NTUEE-ESLab/2017Fall-SmartCameraCar/flask-video-streaming/frame.jpg

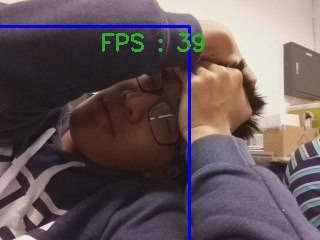
flask-video-streaming/frame.jpg
