NTUEE-ESLab/2017Fall-SmartCameraCar/Tracker_c_program/frame.jpg

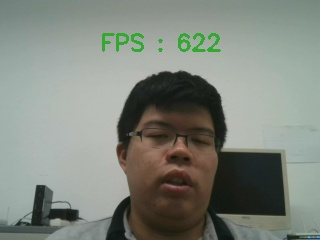
Tracker_c_program/frame.jpg
