NTUEE-ESLab/2017Fall-SmartCameraCar/webpage/images/automatic.jpg

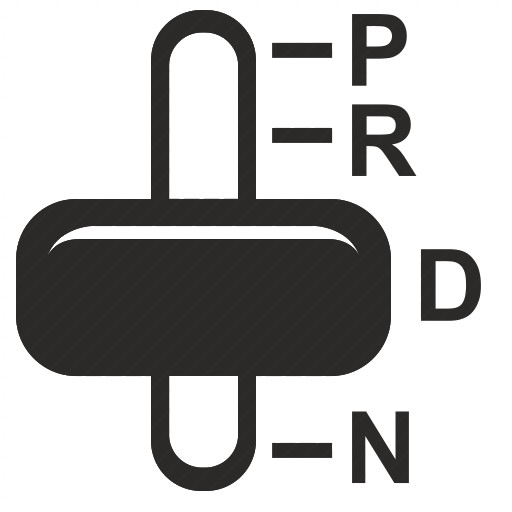
webpage/images/automatic.jpg
