NTUEE-ESLab/2017Fall-SmartCameraCar/webpage/images/cradle_head.jpg

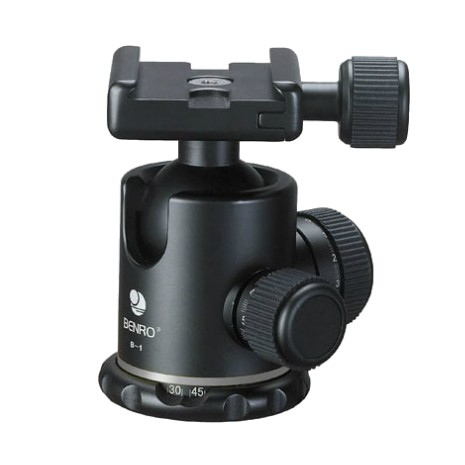
webpage/images/cradle_head.jpg
