NTUEE-ESLab/2017Fall-SmartCameraCar/webpage/images/cta01.jpg

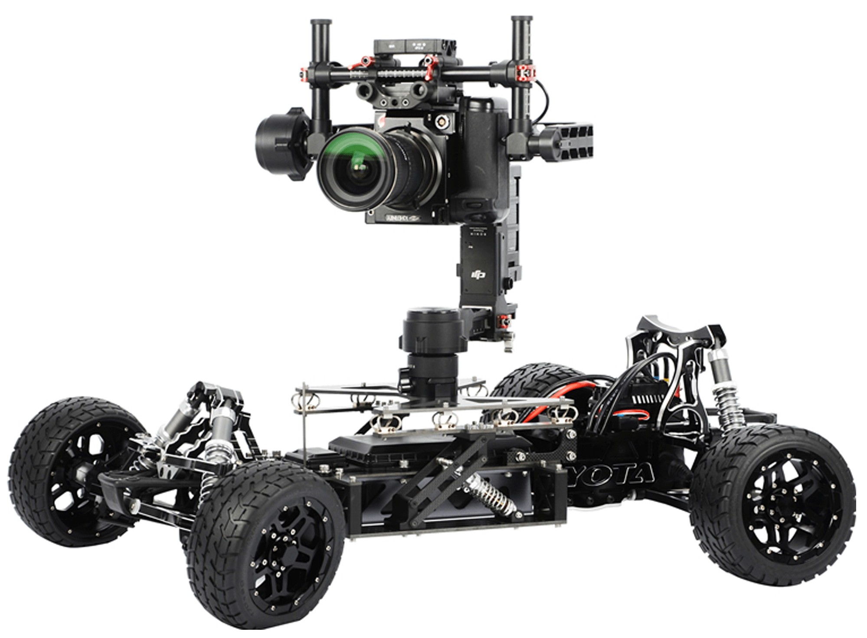
webpage/images/cta01.jpg
