NTUEE-ESLab/2017Fall-SmartCameraCar/webpage/images/darknet.png

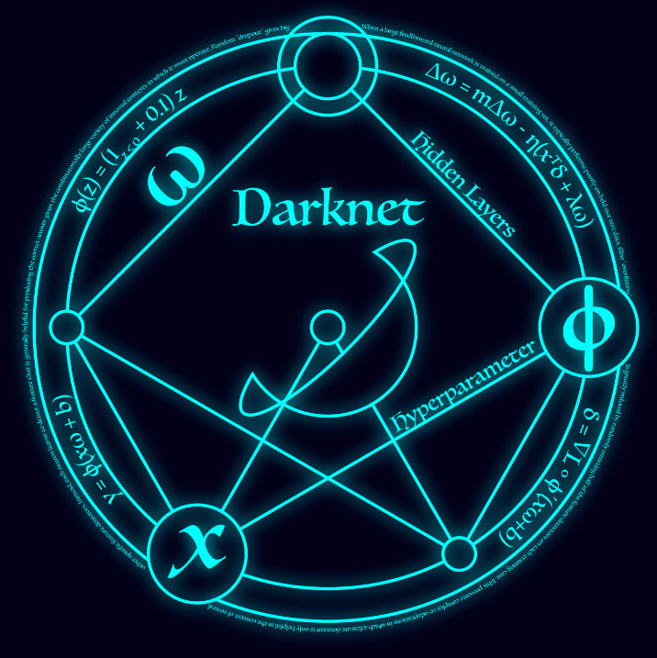
webpage/images/darknet.png
