NTUEE-ESLab/2017Fall-SmartCameraCar/webpage/images/darknet_run.png

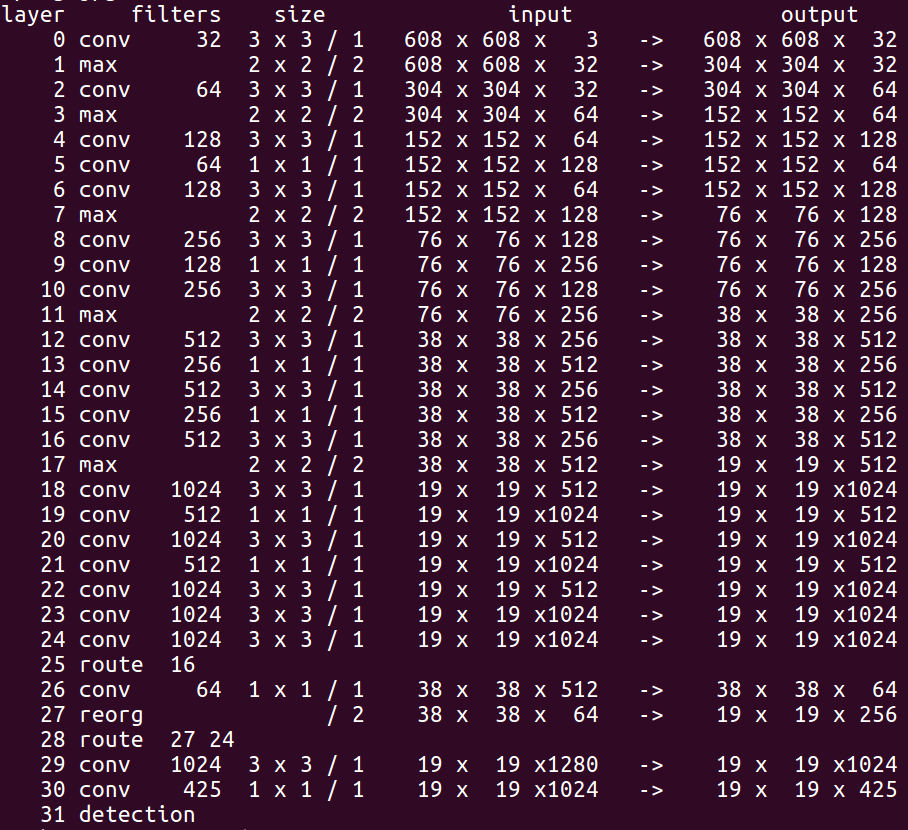
webpage/images/darknet_run.png
