NTUEE-ESLab/2017Fall-SmartCameraCar/webpage/images/gallery/02.jpg

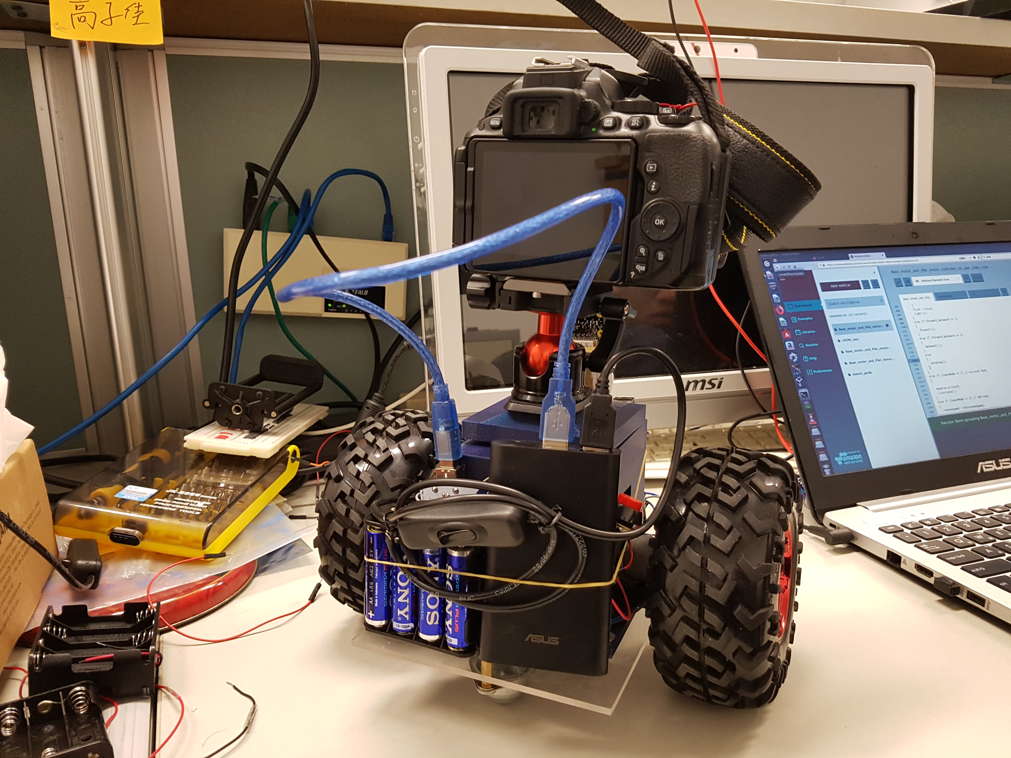
webpage/images/gallery/02.jpg
