NTUEE-ESLab/2017Fall-SmartCameraCar/webpage/images/gallery/03.jpg

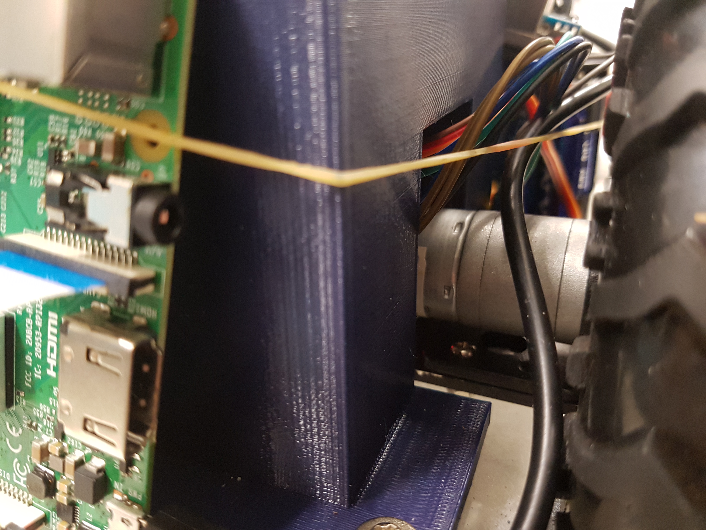
webpage/images/gallery/03.jpg
