NTUEE-ESLab/2017Fall-SmartCameraCar/webpage/images/gallery/04.jpg

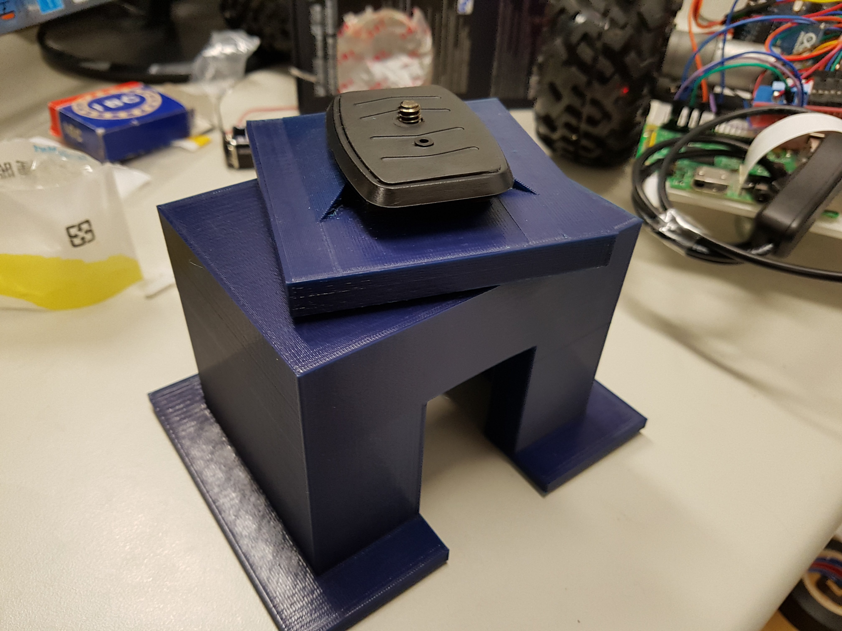
webpage/images/gallery/04.jpg
