NTUEE-ESLab/2017Fall-SmartCameraCar/webpage/images/gallery/05.jpg

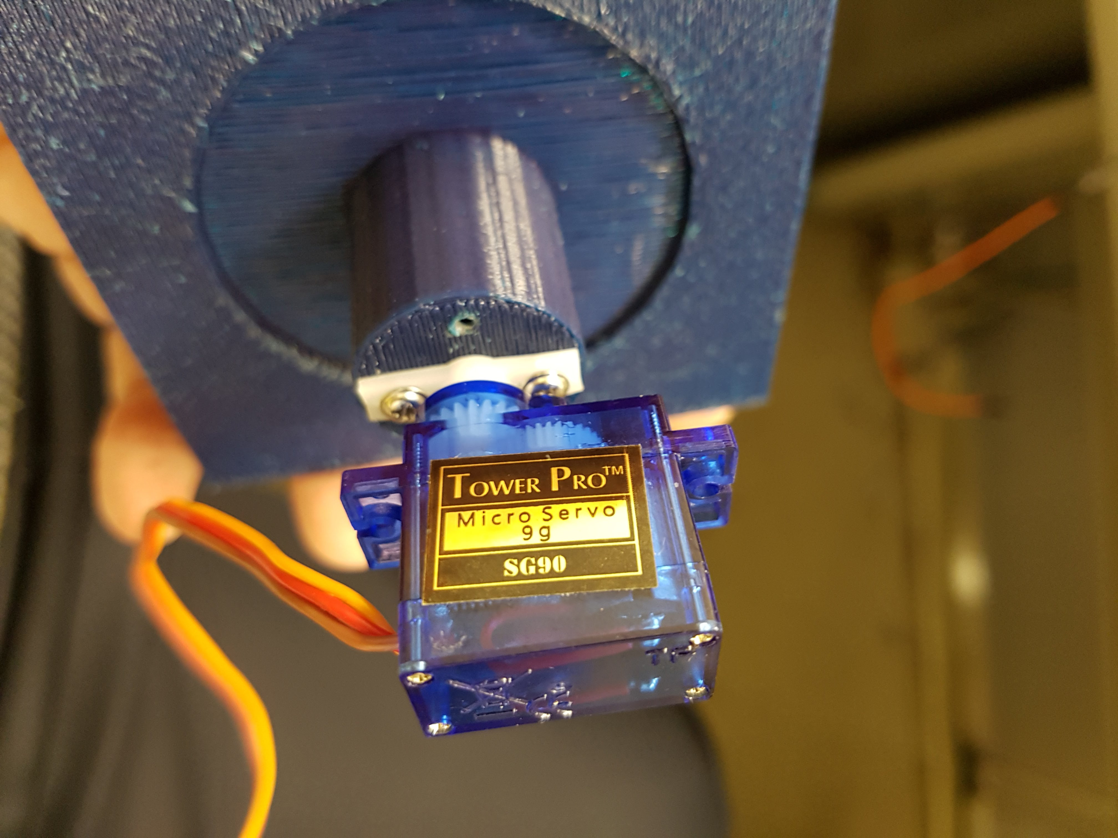
webpage/images/gallery/05.jpg
