NTUEE-ESLab/2017Fall-SmartCameraCar/webpage/images/gallery/06.jpg

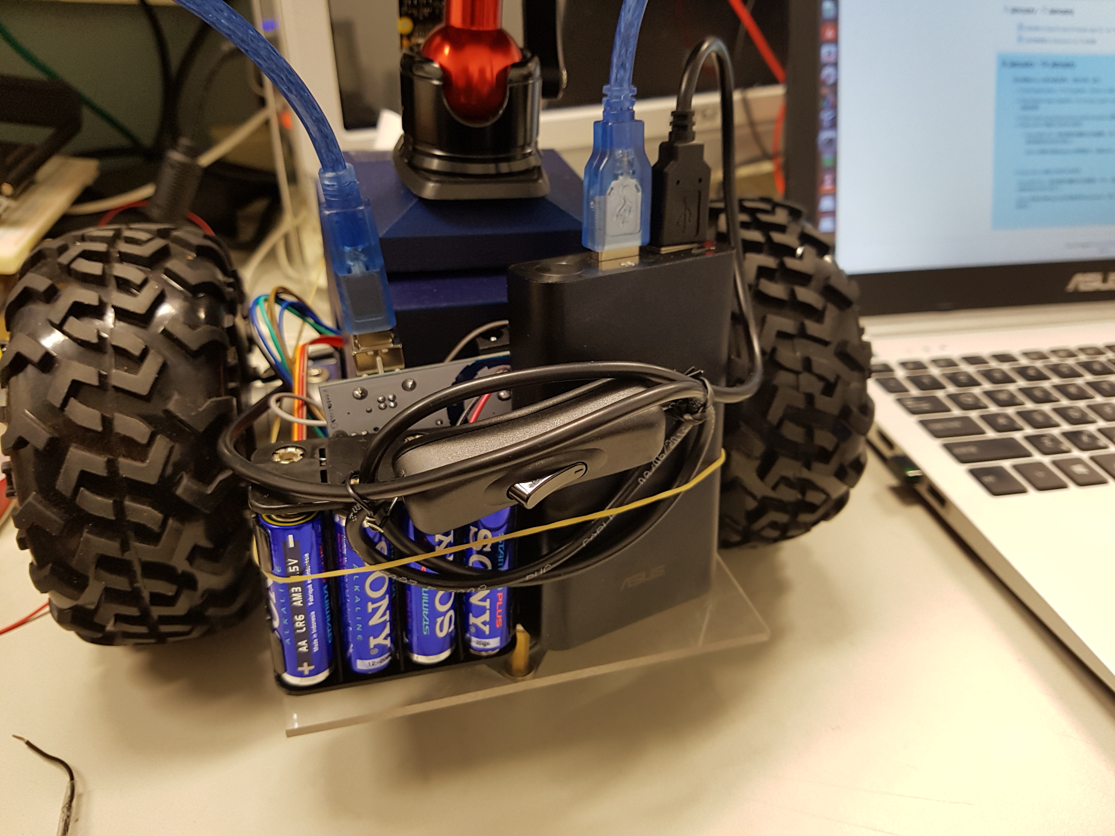
webpage/images/gallery/06.jpg
