NTUEE-ESLab/2017Fall-SmartCameraCar/webpage/images/gallery/07.jpg

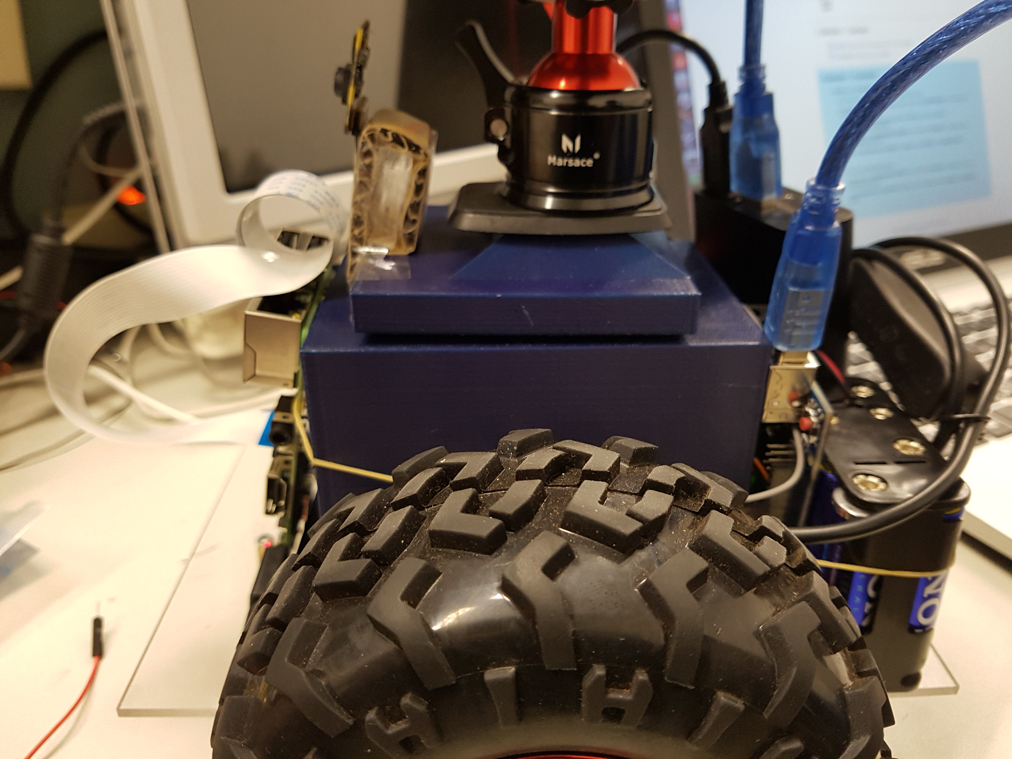
webpage/images/gallery/07.jpg
