NTUEE-ESLab/2017Fall-SmartCameraCar/webpage/images/gallery/08.jpg

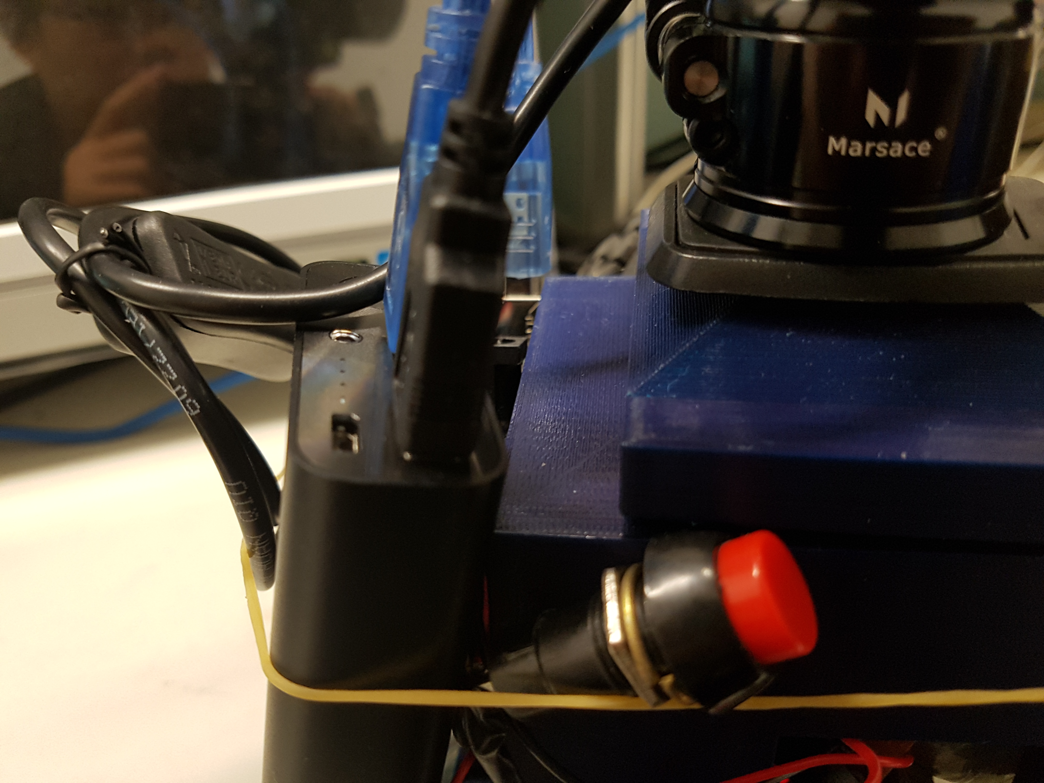
webpage/images/gallery/08.jpg
