NTUEE-ESLab/2017Fall-SmartCameraCar/webpage/images/gallery/09.jpg

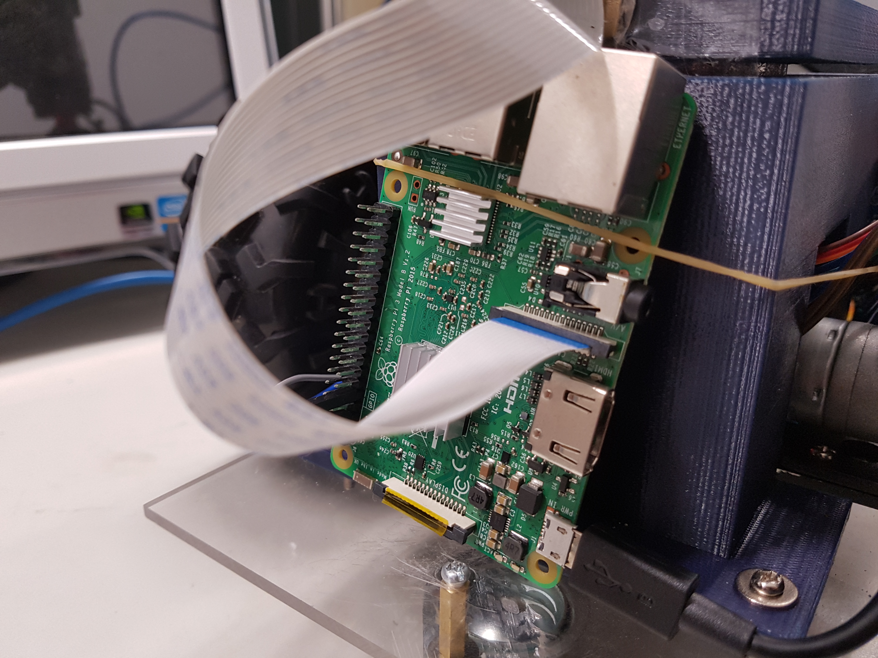
webpage/images/gallery/09.jpg
