NTUEE-ESLab/2017Fall-SmartCameraCar/webpage/images/gallery/10.jpg

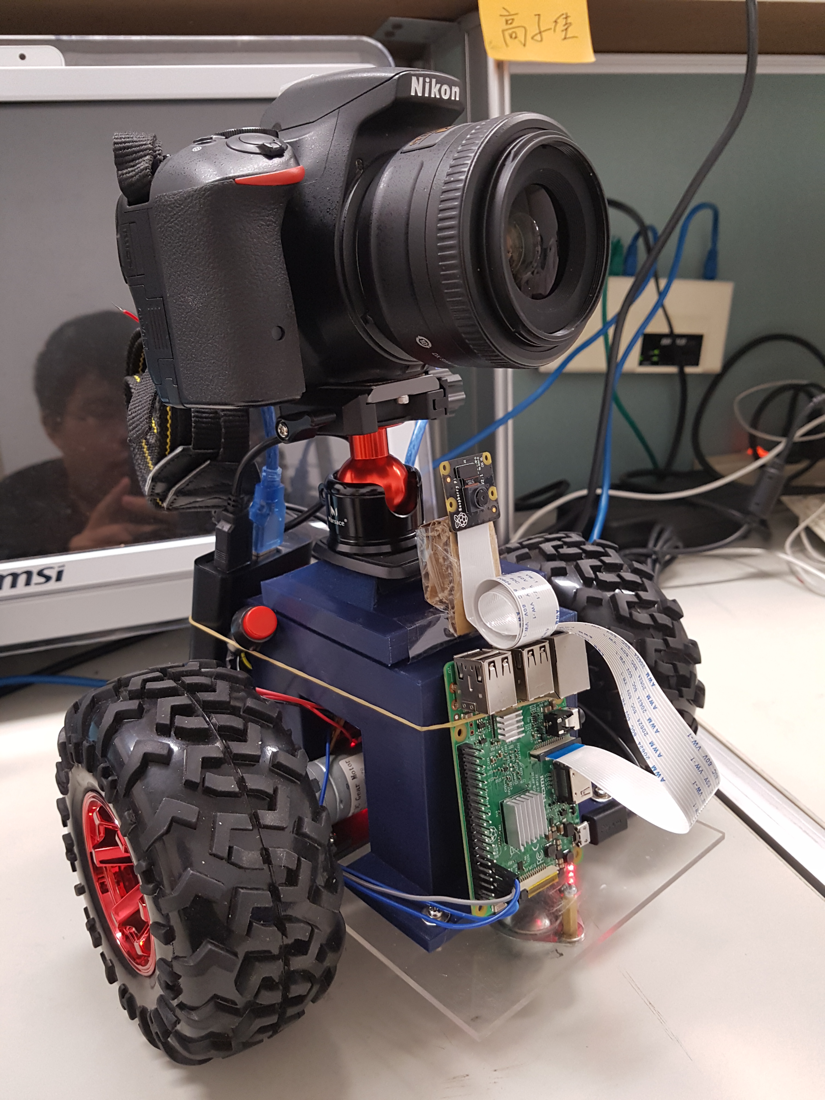
webpage/images/gallery/10.jpg
