NTUEE-ESLab/2017Fall-SmartCameraCar/webpage/images/gallery/12.jpg

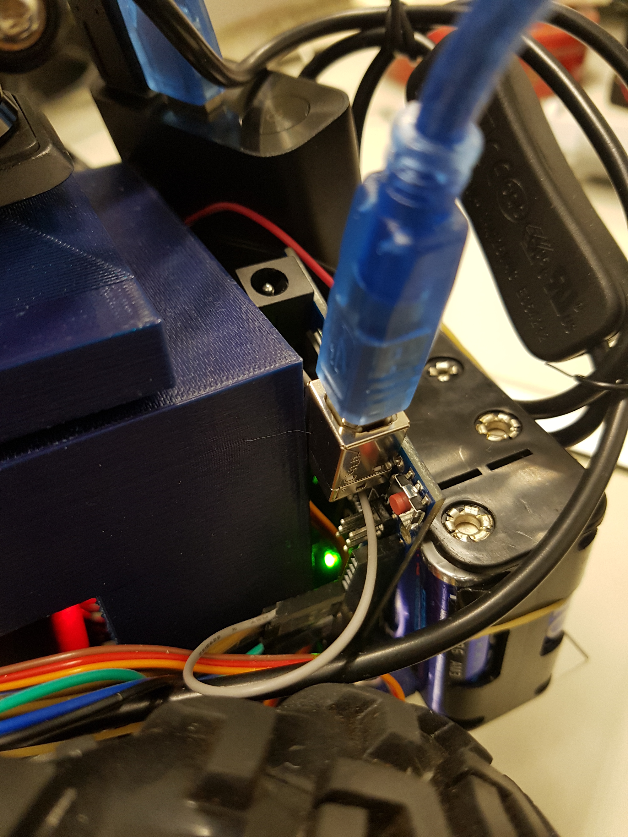
webpage/images/gallery/12.jpg
