NTUEE-ESLab/2017Fall-SmartCameraCar/webpage/images/kaoben.jpg

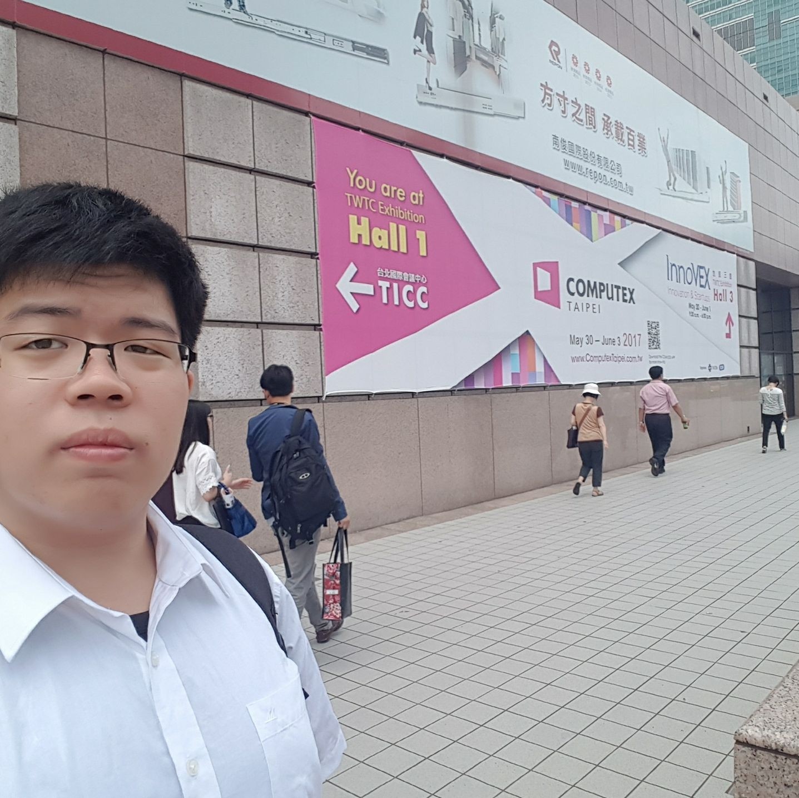
webpage/images/kaoben.jpg
