NTUEE-ESLab/2017Fall-SmartCameraCar/webpage/images/MediamFlowTracker.png

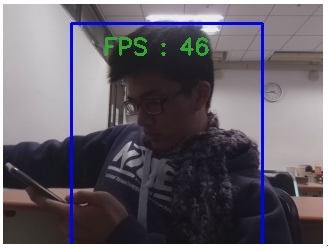
webpage/images/MediamFlowTracker.png
