NTUEE-ESLab/2017Fall-SmartCameraCar/webpage/images/money.jpg

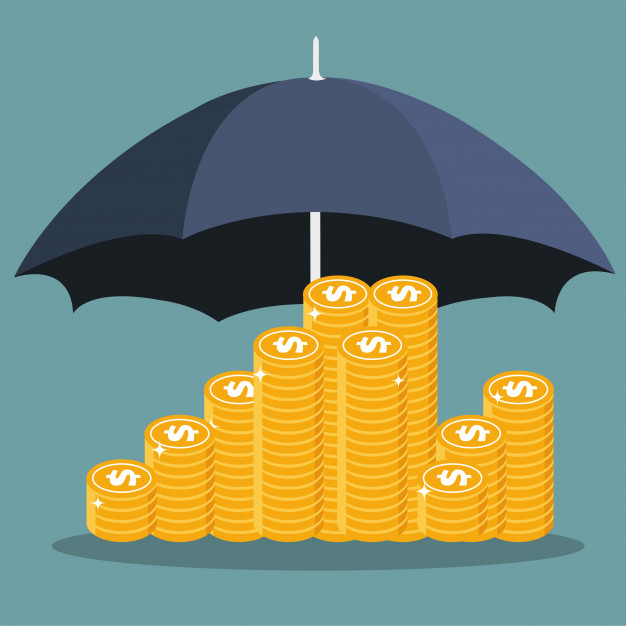
webpage/images/money.jpg
