NTUEE-ESLab/2017Fall-SmartCameraCar/webpage/images/our_car_detect.png

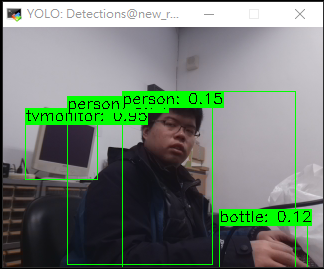
webpage/images/our_car_detect.png
