NTUEE-ESLab/2017Fall-SmartCameraCar/webpage/images/SmartCameraCar.jpg

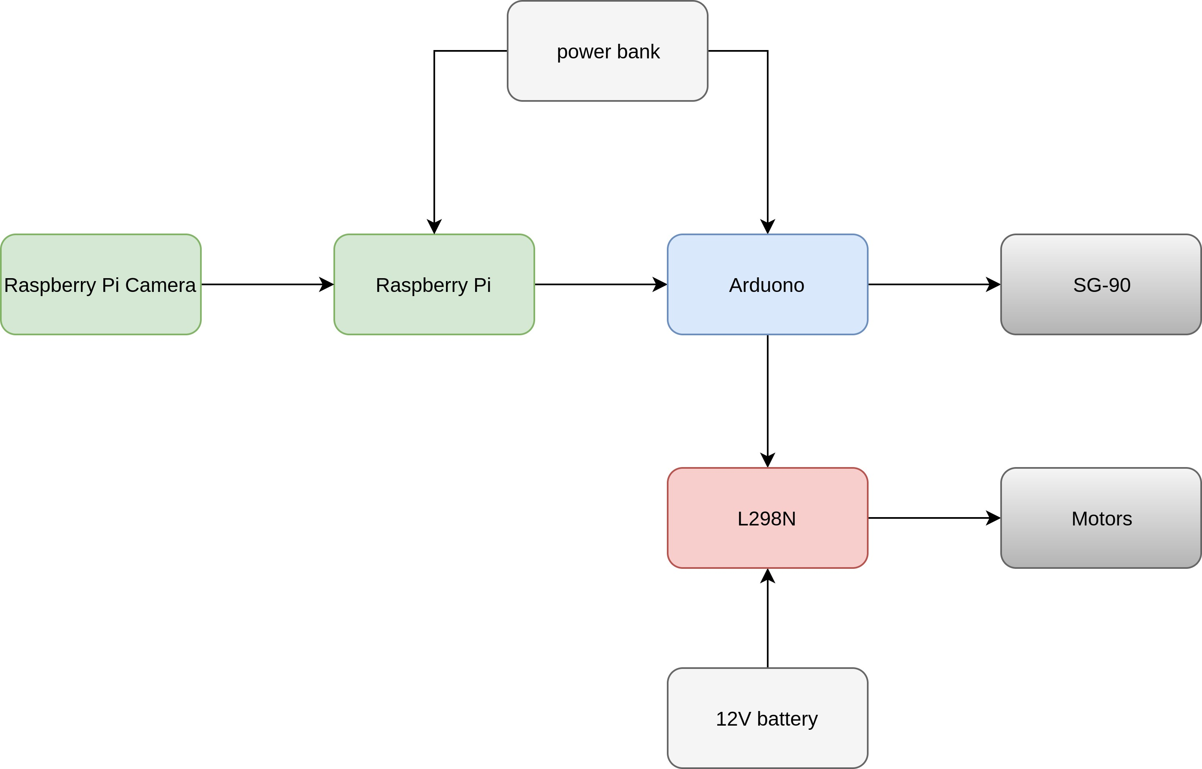
webpage/images/SmartCameraCar.jpg
