NTUEE-ESLab/2017Fall-SmartCameraCar/webpage/images/smooth.jpg

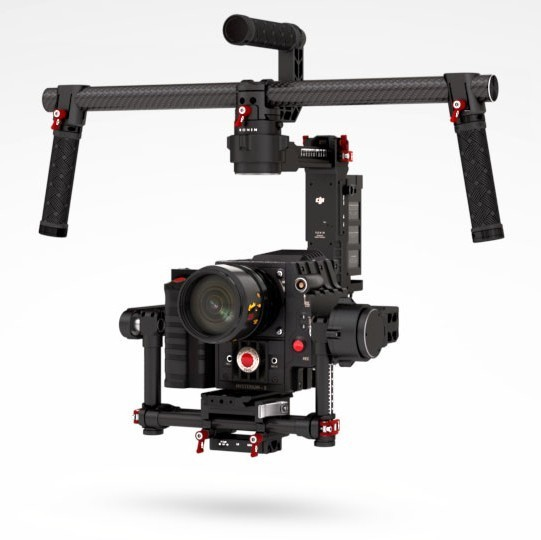
webpage/images/smooth.jpg
