NTUEE-ESLab/2017Fall-SmartCameraCar/webpage/images/thrust_bearing.jpg

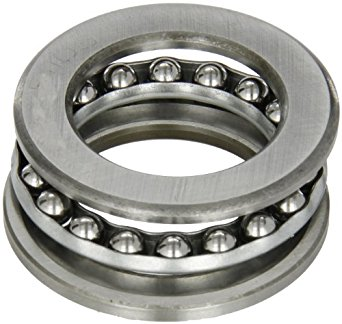
webpage/images/thrust_bearing.jpg
