NTUEE-ESLab/2017Fall-SmartCameraCar/webpage/images/thumbs/11.jpg

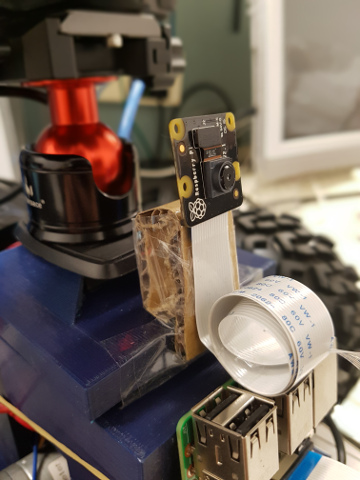
webpage/images/thumbs/11.jpg
