NTUEE-ESLab/2017Fall-SmartCameraCar/webpage/images/tiny_yolo_detect.png

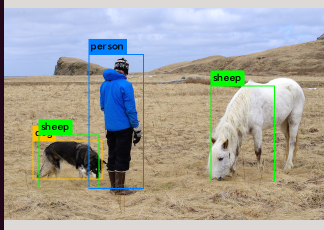
webpage/images/tiny_yolo_detect.png
