NTUEE-ESLab/2017Fall-SmartCameraCar/webpage/images/warmtub.jpg

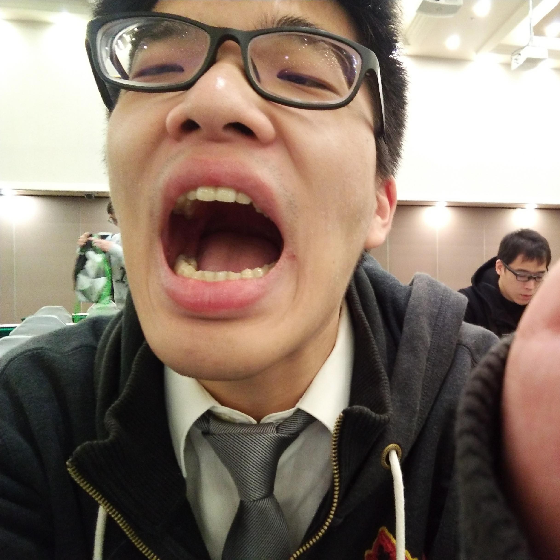
webpage/images/warmtub.jpg
