NTUEE-ESLab/2017Fall-SmartCameraCar/webpage/images/web_monitoring.png

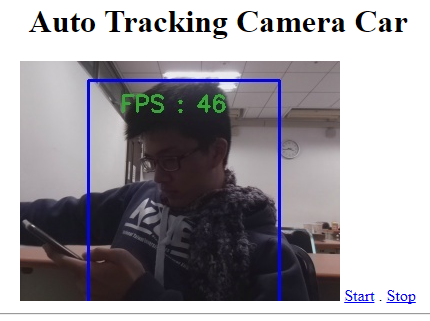
webpage/images/web_monitoring.png
