NTUEE-ESLab/2017Fall-SmartCameraCar/webpage/images/yolo.png

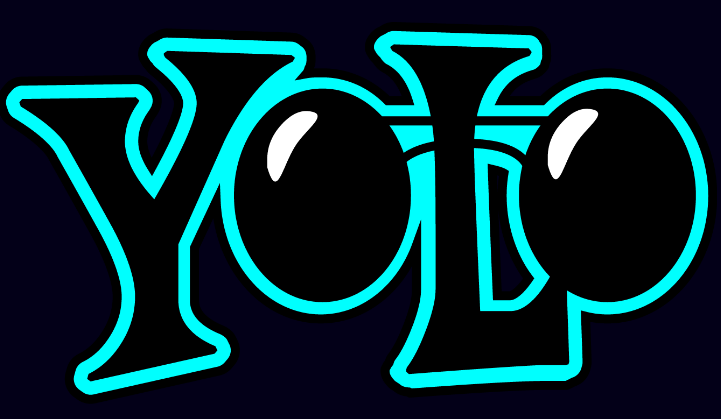
webpage/images/yolo.png
