NTUEE-ESLab/2017Fall-SmartCameraCar/webpage/images/step1-1.jpg

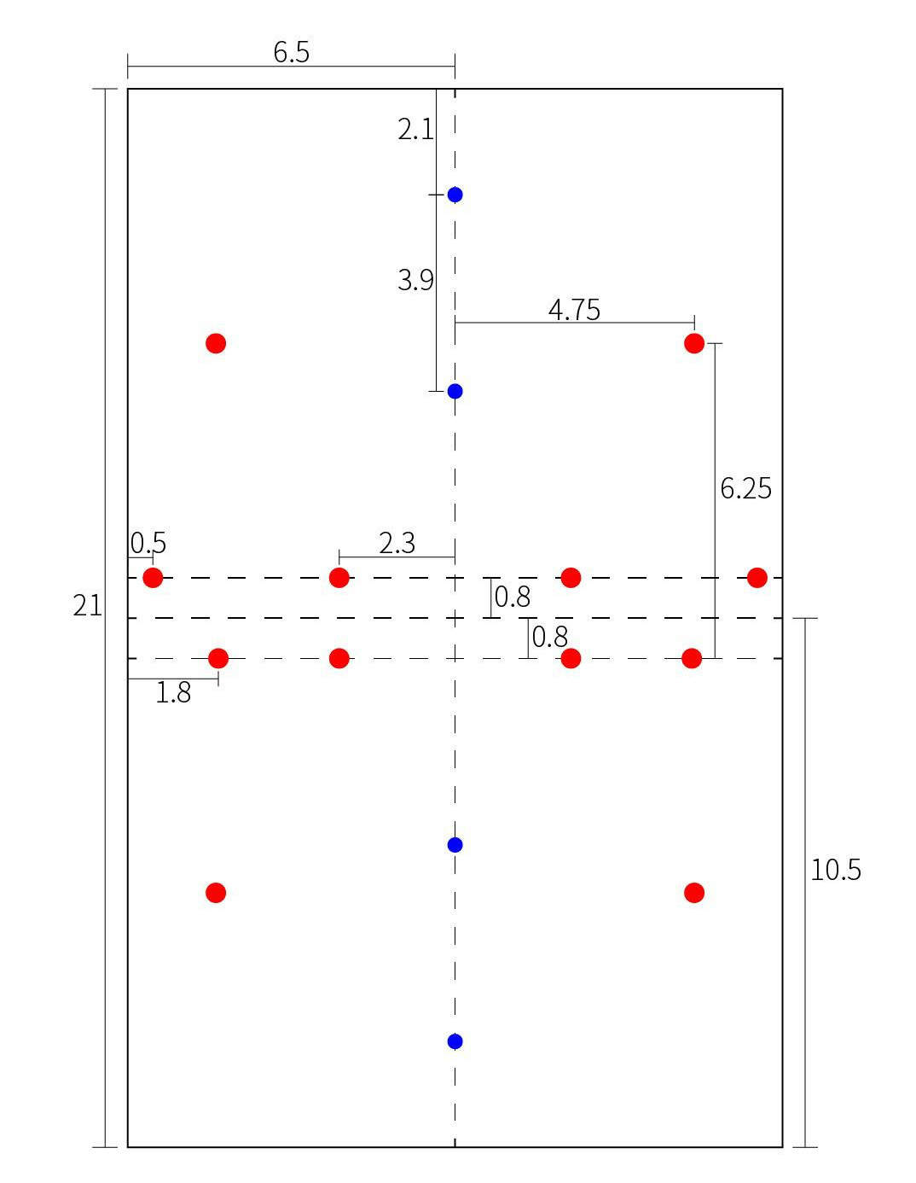
webpage/images/step1-1.jpg
