NTUEE-ESLab/2017Fall-SmartCameraCar/webpage/images/step2.jpg

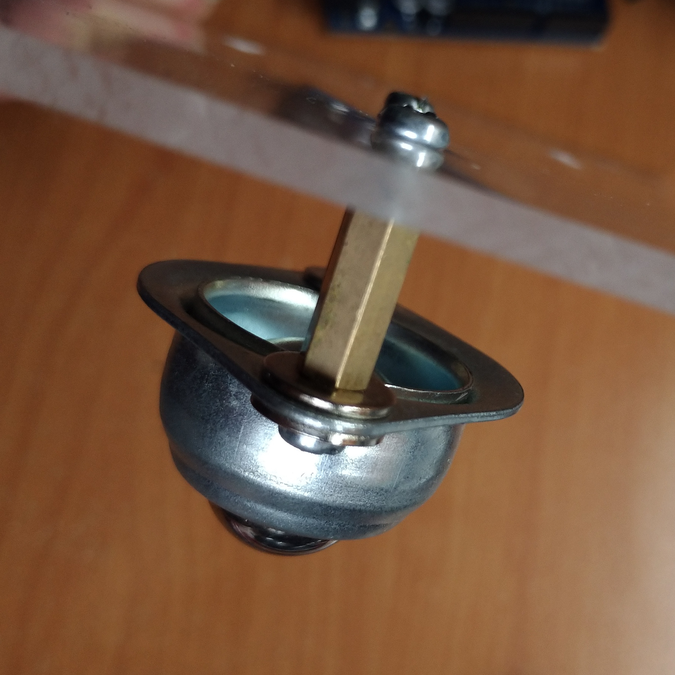
webpage/images/step2.jpg
