NTUEE-ESLab/2017Fall-SmartCameraCar/webpage/images/step6-1.jpg

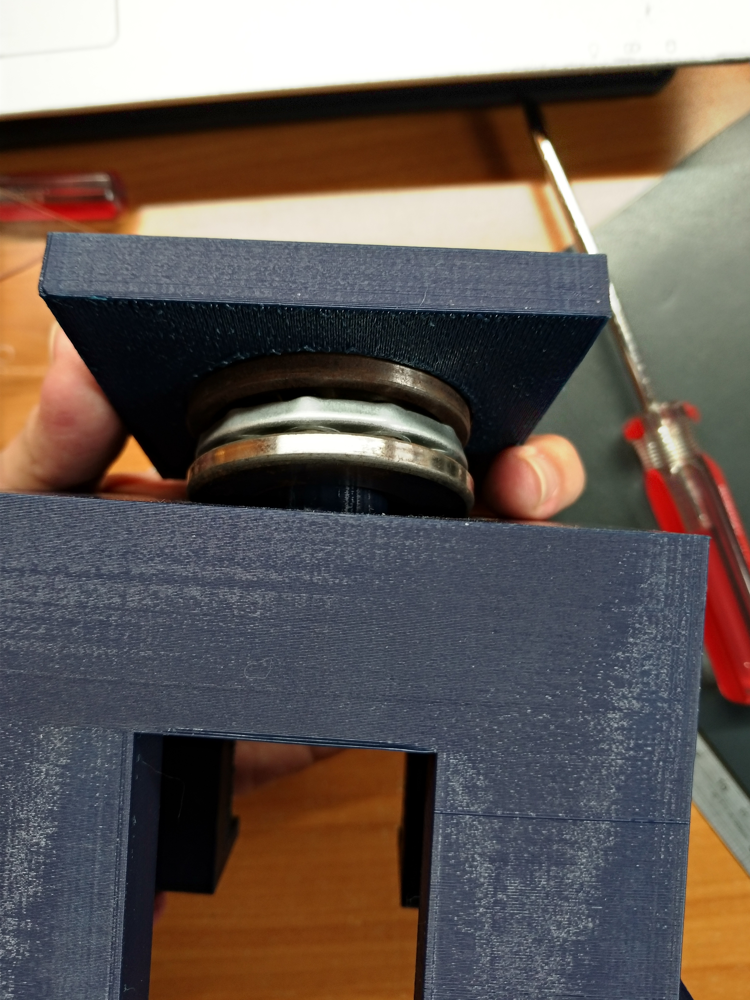
webpage/images/step6-1.jpg
