NTUEE-ESLab/2017Fall-SmartCameraCar/webpage/images/step7.jpg

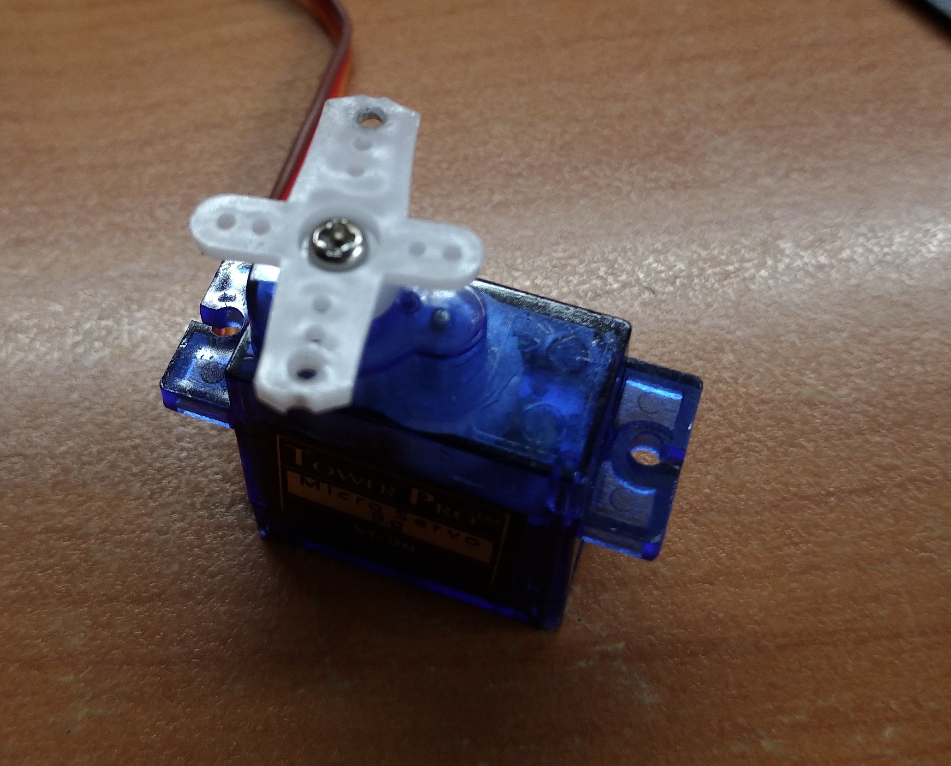
webpage/images/step7.jpg
