NTUEE-ESLab/2017Fall-SmartCameraCar/webpage/images/step9.jpg

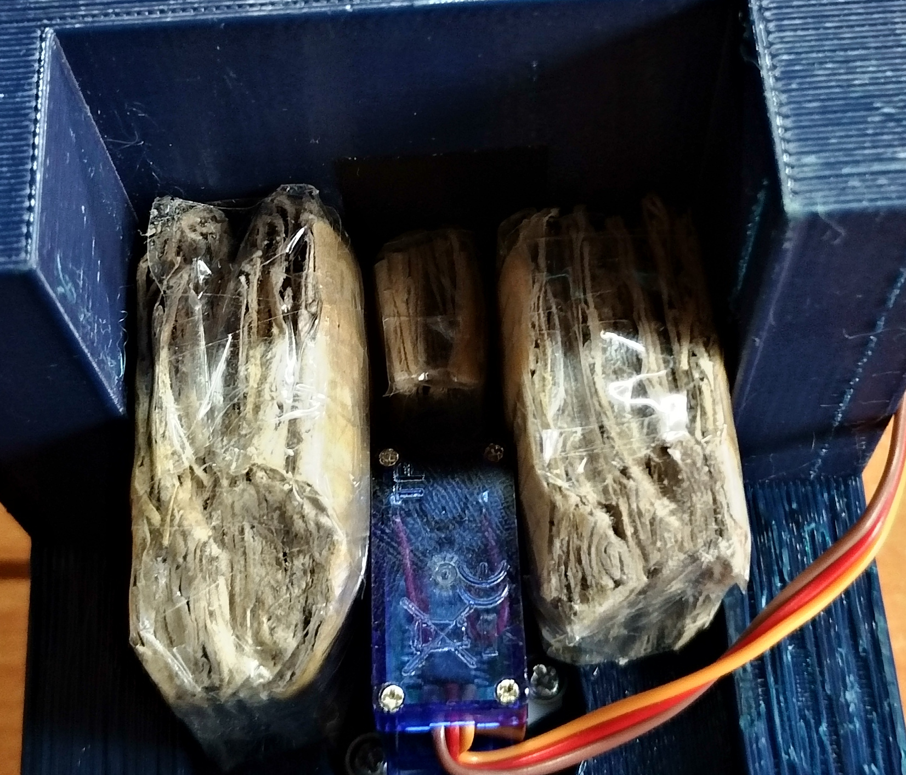
webpage/images/step9.jpg
