NTUEE-ESLab/2017Fall-SmartCameraCar/webpage/images/step11.jpg

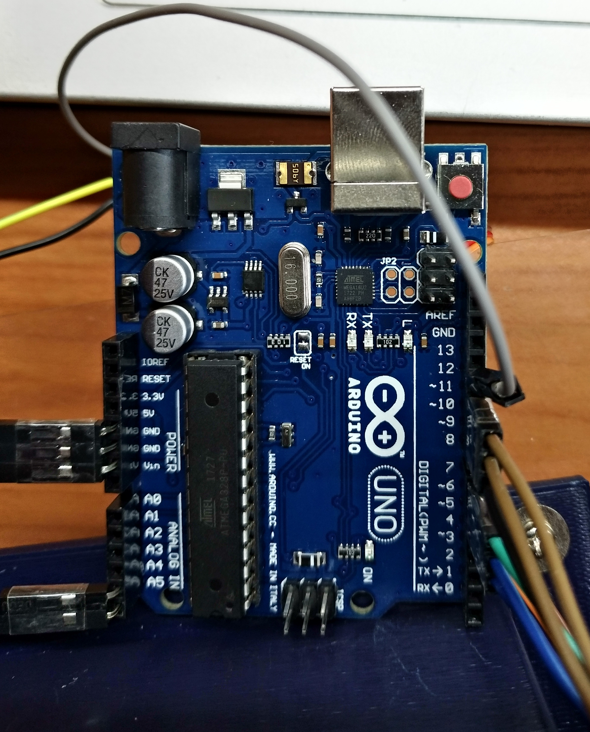
webpage/images/step11.jpg
