NTUEE-ESLab/2017Fall-SmartCameraCar/webpage/images/step13.jpg

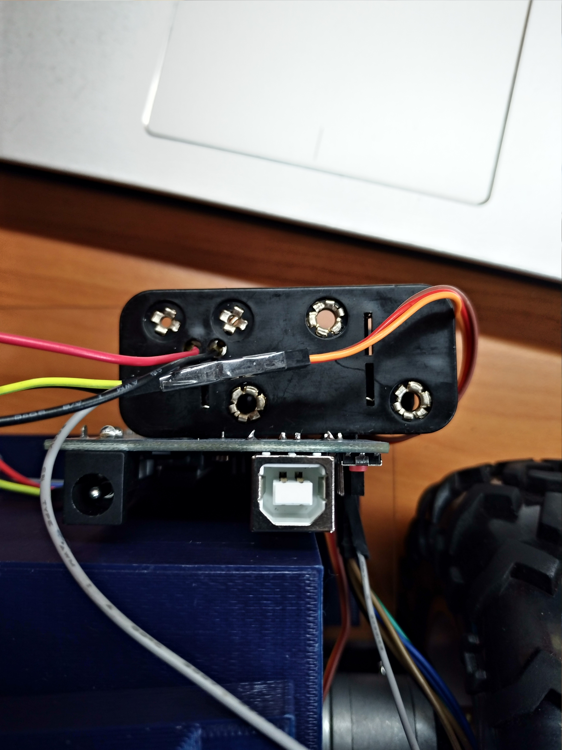
webpage/images/step13.jpg
