NTUEE-ESLab/2017Fall-SmartCameraCar/i2c-pi-arduino.c

#include <unistd.h>
#include <errno.h>
#include <stdio.h>
#include <stdlib.h>
#include <linux/i2c-dev.h>
#include <sys/ioctl.h>
#include <fcntl.h>
#include <unistd.h>
// The arduino board i2c address (slave)
#define ADDRESS 0x04
// The I2C bus: This is for V2 pi's. For V1 Model B you need i2c-0
static const char *devName = "/dev/i2c-1";
int main(int argc, char** argv)
{
        int file, num;
        printf("I2C: Connecting\n");
        if ((file = open(devName, O_RDWR)) < 0)
        {
                fprintf(stderr, "I2C: Failed to access %d\n", devName);
                exit(1);
        }
        printf("I2C: acquiring buss to 0x%x\n", ADDRESS);
        if (ioctl(file, I2C_SLAVE, ADDRESS) < 0)
        {
                fprintf(stderr, "I2C: Failed to acquire bus access/talk to slavee 0x%x\n", ADDRESS);
                exit(1);
        }
        printf("Please enter direction: (1 for forward, 2 for backward, 3 for right, 4 for left, others for stop): ");
        while (scanf("%d", &num) == 1) {
                printf("Sending %d\n", num);
                if (write(file, &num, 1) == 1) {
                        usleep(100000);
                }
        }
}
